FelixMTP/Neko-CO2/Capteur_neko_calib_wifi/Capteur_neko_calib_wifi.ino

#include "esp_timer.h"
#include <Wire.h>
#include <SparkFun_SCD30_Arduino_Library.h>
#include <WiFi.h>
#include <WebServer.h>
// Download the SeeedStudio SCD30 Arduino driver here:
//  => https://github.com/Seeed-Studio/Seeed_SCD30/releases/latest
//#include "SCD30.h"
//#include "Sensirion_GadgetBle_Lib.h"
#include <EasyBuzzer.h>

static int64_t lastMmntTime = 0;
static int startCheckingAfterUs = 1900000;
int compteur = 0; // Compteur à ne pas modifier, sert à compter le nombre de bip

// Paramètres Wifi :
const char* ssid = "Nom du réseau Wifi";            // Entrer ici le SSID du réseau wifi auquel le capteur doit se connecter. Laisser les " "
const char* pwd = "mot de passe du reseau wifi";    // Entrer ici le mot de passe du réseau wifi auquel le capteur doit se connecter. Laisser les " "

// Paramètres de calibration 
String cal_passwort = "test"; // Mot de passe de calibration

// Paramètres à modifier en fonction de votre montage :
#define SDA_pin 26  // Define the SDA pin used for the SCD30
#define SCL_pin 27  // Define the SCL pin used for the SCD30
int ledR = 19;      // Pin de la led rouge
int ledO = 18;      // Pin de la led orange ou jaune
int ledV = 5;       // Pin de la led verte
int ledB = 17;      // Pin de la led bleue
int pin = 25;       // Pin du Buzzer
int autocalib = 0;  // Mettre à 1 si vous voulez utiliser la fonction d'autocalibration ou 0 si vous voulez utiliser une calibration à taux forcé
int valeur_calib = 400; // Mettre ici le taux de CO2 servant à la calibration à taux forcé

// Parametres du BUZZER
int nbip = 3; // Modifier ici le nombre de bip souhaités
int hz = 440; // Définir ici la fréquence du son souhaité
int duree = 1000; // Définir ici la durée du bip souhaitée (pas garanti que ça fonctionne en cas de modification)

String matrixausgabe_text  = " "; // Ausgabetext als globale Variable
volatile int matrixausgabe_index = 0;// aktuelle Position in Matrix
IPAddress myOwnIP; // ownIP for mDNS 
int CO2 = 0 ;
//Reading CO2, humidity and temperature from the SCD30 By: Nathan Seidle SparkFun Electronics
//https://github.com/sparkfun/SparkFun_SCD30_Arduino_Library

// fonction de calibration manuelle
SCD30 airSensorSCD30; // Objekt SDC30 Umweltsensor
int doCal=0;  // Kalibriermerker
int input_valcalib = 430; //valeur de calibration par défaut
void CO2_Kalibrierfunktion(int valeur){ // Kalibrierfunktion
// Forced Calibration Sensirion SCD 30
  Serial.print("Start SCD 30 calibration, please wait 20 s ...");delay(20000);
  airSensorSCD30.setAltitudeCompensation(0); // Altitude in m ü NN 
  airSensorSCD30.setForcedRecalibrationFactor(valeur); // fresh air 
  Serial.println(" done");
}

WebServer server(80);  // Permet l'affichage de la page d'accueil 
//------------------------------ Server Hompage html-Code
const char INDEX_HTML_START[] =
 "<!DOCTYPE HTML>"
  "<html>"
  "<META HTTP-EQUIV=\"refresh\" CONTENT=\"20\">"
   "<head>"
   "<meta name = \"viewport\" content = \"width = device-width, initial-scale = 1.0, maximum-scale = 1.0, user-scalable=0\">"
     "<title>IoT-Werkstatt Umwelt-Campus Birkenfeld</title>"
   "</head>"
    "<body>"
    "<CENTER>";

const char INDEX_HTML_SUBMIT[] =
     "<FORM action=\"/\" method=\"post\">"
     "<P>"
        "Mot de passe de calibration : "
        "<INPUT type=\"text\" name=\"message\"><br>"
        "Valeur de calibration : "
        "<INPUT type=\"text\" name=\"valcalib\">"
        "<INPUT type=\"submit\" value=\"Calibrate\">"
      "</P>"
     "</FORM>";

String cal_message  = "Entrez le mot de passe de calibration";      // Nachricht
 
const char INDEX_HTML_END[] =
    "</CENTER>"
   "</body>"
  "</html>";
 
//------------------------------ Server Ausgabe Messwerte in Form einer html-Tabelle

String messwertTabelle(){ 
  String unit1=" C";
  String unit2=" %";
  String unit3="";

  String nam1="Temperature";
  String nam2="Humidite";
  String nam3="";

  float mess1=airSensorSCD30.getTemperature();
  float mess2=airSensorSCD30.getHumidity();
  float mess3=0;
  //String html =  "<h2>Aktuelle Informationen:</h2>";
  String html = "<h2><table>";
  if (nam1.length()>0)
     html = html +  "<tr><td>" + nam1 + ":</td> <td>" + String(mess1) + "</td><td>"+ unit1 +" </td></tr>";
  if (nam2.length()>0)
     html = html +  "<tr><td>" + nam2 + ":</td> <td>" + String(mess2) + "</td><td>"+ unit2 +" </td></tr>";
  if (nam3.length()>0)
     html = html +  "<tr><td>" + nam3 + ":</td> <td>" + String(mess3) + "</td><td>"+ unit3 +" </td></tr>";
  html=html+"</table></h2>";
  return html;
}
//------------------------------ Server Ausgabe Bild in Abhängigkeit von Messert und Grenzen
void serverSendFigure(){ 
  String unit ="ppm";
  String nam  ="CO2";
  float mess=CO2;
  float limit1 = 800;
  float limit2 = 1400;
  if (mess < limit1) // grün
     server.sendContent(F("<img src= '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'alt=''>"));
    else
     if (mess>limit2) // rot 
        server.sendContent(F("<img src='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' alt=''>"));
       else // gelb
        server.sendContent(F("<img src='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' alt=''>"));
     String val = String("<h1>")+String(nam)+String(": ")+String(mess)+String(" ")+unit+ String("</h1>");
     server.sendContent(val);
 }
//------------------------------ Server Unterprogramm zur Bearbeitung der Anfragen
void serverHomepage() { 
 if (server.hasArg("message")) {// Wenn Kalibrierpasswort eingetroffen,
   String input = server.arg("message");     // dann Text vom Client einlesen
   input_valcalib = server.arg("valcalib").toInt();     // dann Text vom Client einlesen

   if (input == cal_passwort){
      cal_message = "Calibration en cours (patientez environ 20s)...";
      doCal = 1;
   } else
      cal_message = "Mauvais mot de passe";
 } else cal_message = "";
   server.setContentLength(CONTENT_LENGTH_UNKNOWN);
 server.send ( 200, "text/html", INDEX_HTML_START);
 serverSendFigure();             // Ampel integrieren
 server.sendContent(F("<img src=' 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' alt=''>"));
 server.sendContent(messwertTabelle());
 //if (cal_passwort != "test") {
  server.sendContent(INDEX_HTML_SUBMIT);
  server.sendContent(cal_message);
 //}
 server.sendContent(INDEX_HTML_END);
}

void setup() {
  Serial.begin(115200);
  delay(1000);
  
  pinMode(ledR, OUTPUT);
  pinMode(ledO, OUTPUT);
  pinMode(ledV, OUTPUT);
  pinMode(ledB, OUTPUT);
  
  EasyBuzzer.setPin(pin);

  Serial.println("Demarrage");
  Serial.println("\n");
  WiFi.begin(ssid, pwd);  // Initialisation du Wifi
  Serial.print("Attente de connexion ...");
  while (WiFi.status() != WL_CONNECTED)
  {
    Serial.print(".");
    delay(100);
  }

  Serial.println("\n");  // Affichage "Connexion établie" et de l'adresse IP
  Serial.println("Connexion etablie !");
  Serial.print("Adresse IP: ");
  Serial.println(WiFi.localIP());

  server.on("/", serverHomepage);  // Chargement de la page d'accueil
  server.begin();  // Initialisation du serveur web
  Serial.println("Serveur web actif");

  // Initialize the SCD30 driver
  Serial.println("Initialisation du driver");
  Wire.begin(SDA_pin, SCL_pin);
  
  // Initialize sensor
  Serial.println("Initialisation du sensor");
  if (airSensorSCD30.begin() == false) {
    Serial.println("The SCD30 did not respond. Please check wiring.");
    while(1) {yield(); delay(1);}
  }

  //désactivation de l'autocalibration
  Serial.println("Désactivation de l'autocalibration");
  airSensorSCD30.setAutoSelfCalibration(false); // Sensirion no auto calibration
  airSensorSCD30.setMeasurementInterval(2000);     // CO2-Messung alle 5 s
}

void loop() {

  CO2 = airSensorSCD30.getCO2() ;
  Serial.print("CO2:"+String(String(CO2)));
  Serial.println();
  webpage();

// Provide the sensor values for Tools -> Serial Monitor or Serial Plotter
//  Serial.print("CO2[ppm] : ");
//  Serial.print(CO2);
// Serial.print("ppm \t");
// EasyBuzzer.update();

  if (CO2 < 430){       // S'il y a moins de 430 ppm de CO2
    digitalWrite(ledB,HIGH);    // on allume la led bleue
    digitalWrite(ledV,LOW);
    digitalWrite(ledO,LOW);
    digitalWrite(ledR,LOW);
    compteur =0;                // on remet à zéro le compteur pour que le buzzer puisse sonner à nouveau
  }
  else if (CO2 < 800 && CO2 >= 430){     // S'il y a entre 430 et 800 ppm de CO2
    digitalWrite(ledB,LOW);
    digitalWrite(ledV,HIGH);                           // on allume la led verte
    digitalWrite(ledO,LOW);
    digitalWrite(ledR,LOW);
    compteur =0;                                       // on remet à zéro le compteur pour que le buzzer puisse sonner à nouveau
  }
  else if (CO2 >= 800 && CO2 < 1500){    // S'il y a entre 800 et 1500 ppm de CO2
    digitalWrite(ledB,LOW);
    digitalWrite(ledO,HIGH);                           // on allume la led orange ou jaune
    digitalWrite(ledV,LOW);
    digitalWrite(ledR,LOW);
    // Déplacer ici les lignes correspondant à la sonnerie du buzzer si besoin qu'il sonne dès la limite de 800ppm
    // Fin des lignes à déplacer
    // + Commenter la ligne suivante si le buzzer doit sonner dès la limite de 800ppm
    compteur =0; // on remet à zéro le compteur pour que le buzzer puisse sonner à nouveau
  }
  else if (CO2 >= 1500){    // Si on dépasse les 1500 ppm de CO2
    digitalWrite(ledB,LOW);
    digitalWrite(ledR,HIGH);        // on allume la led rouge
    digitalWrite(ledO,LOW);
    digitalWrite(ledV,LOW);
                                      // On fait sonner le buzzer

    // Déplacer ces lignes plus haut si le buzzer doit sonner lors du passage de la limite de 800ppm
    if (compteur < nbip) {
      EasyBuzzer.singleBeep(
        hz,  // Frequency in Hertz(HZ)
        duree //durée du beep
      );
      compteur = compteur+1;
      delay(1000);
      EasyBuzzer.stopBeep();
    // Fin des lignes à déplacer
    }
    }

  delay(3000);
}

void webpage() 
{
  //Block------------------------------ HTML-Server
  server.handleClient(); //Homepageanfragen versorgen
  delay(1);
  if (doCal) {
     Serial.print("Calibration à "); Serial.println(input_valcalib);
     CO2_Kalibrierfunktion(input_valcalib); // Kalibrierfunktion aufrufen 
     doCal=0; 
  }
}
